mkilgore/avr-eeprom-programmer/programmer/src/dump_mem.c

#include <stdio.h>
#include <string.h>

#include "dump_mem.h"

void dump_mem(const void *buf, size_t len, uint32_t base_addr)
{
    char strbuf[100], strbuf2[100] = { 0 };
    char *cur_b, *start, *to_print;
    const unsigned char *b = buf;
    int i = 0, j, skipping = 0;

    cur_b = strbuf;
    start = strbuf;

    for (; i < len; i += 16) {
        cur_b += sprintf(cur_b, "0x%08x  ", (i) + base_addr);

        for (j = i; j < 0; j++)
            cur_b += sprintf(cur_b, "   ");

        for (j = i; j < i + 16; j++) {
            if (j < len)
                cur_b += sprintf(cur_b, "%02x ", (const unsigned int)b[j]);
            else
                cur_b += sprintf(cur_b, "   ");
            if (j - i == 7)
                *(cur_b++) = ' ';
        }

        for (j = 0; j < i % 16; j++)
            cur_b += sprintf(cur_b, " ");

        cur_b += sprintf(cur_b, " |");
        for (j = i; j < i + 16 && j < len; j++)
            if (b[j] > 31 && b[j] <= 127)
                cur_b += sprintf(cur_b, "%c", b[j]);
            else
                *(cur_b++) = '.';
        sprintf(cur_b, "|\n");

        to_print = start;

        if (start == strbuf)
            start = strbuf2;
        else
            start = strbuf;

        cur_b = start;

        /* The 12 magic number is just so we don't compare the printed address,
         * which is in '0x00000000' format at the beginning of the string */
        if (strcmp(strbuf + 12, strbuf2 + 12) != 0) {
            if (skipping == 1)
                printf("%s", start);
            else if (skipping == 2)
                printf("...\n");
            skipping = 0;
            printf("%s", to_print);
        } else if (skipping >= 1) {
            skipping = 2;
        } else {
            skipping = 1;
        }
    }
    if (skipping)
        printf("...\n%s", to_print);
}
